enjoy-digital/litex-acorn-baseboard/bringup/standard/acorn_i2c_ecp5/firmware/i2c_spi.h

#include <stdbool.h>
#include <stdint.h>

#define I2C_ADDR 0x28
#define GPIO_WRITE 0xf4
#define GPIO_READ 0xf5
#define GPIO_ENABLE 0xf6
#define GPIO_CONFIG 0xf7
#define CONFIG_SPI 0xf0

bool i2c_spi_write(uint8_t ss, uint8_t *data, unsigned len);
bool i2c_spi_read(uint8_t ss, uint8_t *data, unsigned len);
